MurrayBoz/urbanpotager-v1/object/UrbanPotager - MicroEdition - v4/Arduino/UrbanPotager/chardef.h

#ifndef chardef_h
#define chardef_h

#define CELCIUS_ARRAY {B01000,B10100,B01000,B00011,B00100,B00100,B00011}
#define LIGHT_ARRAY {B00000,B10101,B01110,B11111,B01110,B10101,B00000,B00000}
#define HUMIDITY_ARRAY {B00100,B01110,B11111,B01000,B00010,B01000,B00010,B00000}
#define TEMP_ARRAY {B00100,B01010,B01010,B01110,B11111,B11111,B01110}
#define WATER_ARRAY {B00000,B00100,B01110,B01110,B11111,B11101,B11111,B01110}
#define WATER2_ARRAY {B00100,B01110,B01110,B11111,B11101,B11111,B01110,B00000}

#endif
